saarbastler/RetroNixie/cnc/digits2.png

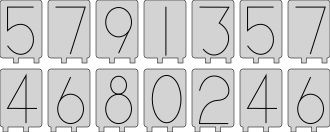
cnc/digits2.png
