saarbastler/RetroNixie/PCB/ClockPCB.png

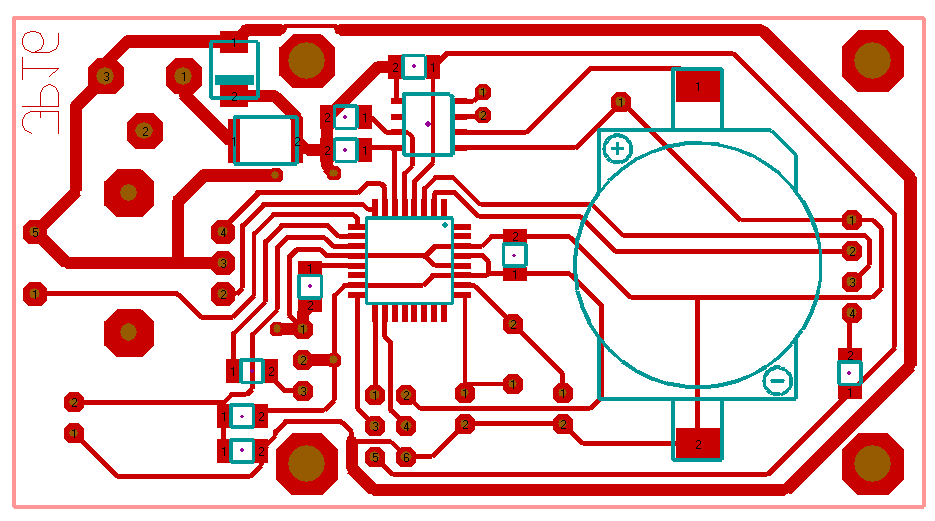
PCB/ClockPCB.png
