saarbastler/RetroNixie/PCB/DotsSegmentPCB.png

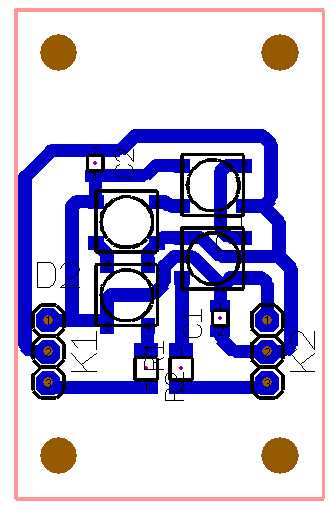
PCB/DotsSegmentPCB.png
